AidanHockey5/MegaMIDI/src/LCDChars.h

#ifndef _LCDCHARS_H_
#define _LCDCHARS_H_

const unsigned char arrowCharRight[8] = 
{
	0b00001,
	0b00011,
	0b00111,
	0b01111,
	0b01111,
	0b00111,
	0b00011,
	0b00001
};

const unsigned char arrowCharLeft[8] = 
{
	0b10000,
	0b11000,
	0b11100,
	0b11110,
	0b11110,
	0b11100,
	0b11000,
	0b10000
};

const unsigned char heartChar[8] = 
{
  B00000,
  B00000,
  B01010,
  B10101,
  B10001,
  B01010,
  B00100,
  B00000
};

const unsigned char arrowCharInvertedRight[] = 
{
	B10000,
	B11000,
	B10100,
	B10010,
	B10010,
	B10100,
	B11000,
	B10000
};

#endif
